tm-treehouse/lyrebird/model/notes-idle.md

# Idle-channel behaviour, and what the element lines do to the reference

Run: `./.venv/bin/python model/run_idle.py`. Logs in `results/idle.txt` and
`results/reference-current.txt`, figures `figures/idle_window.png` and
`figures/idle_blast.png`.

Two findings, in the order they were made. The first closes an open item: the
low-frequency limit cycle was a measurement artifact. The second opens a
larger one: **the element transition rate is a rectified copy of the signal,
it puts a signal-correlated current on the rail that sets full scale, and the
rotation creates that correlation rather than whitening it.** Section H.

## The headline (first finding: the limit cycle)

`notes-programme.md` reached the same conclusion independently and from a
different reproduction, at 96 kHz with one percent elements rather than the
176.4 kHz reference row. Two unrelated routes to the same 12-bin main lobe.

**The 15 to 19 dB loss is a measurement artifact, not a loop fault.** The
tripped run README.md reports at 125.06 dB measures **143.40 dB** when the
*windowed* mean is removed from the same record instead of the arithmetic
mean, and **143.69 dB** when the same trajectory is measured over 2^21 with
nothing else changed. Both agree with the 143.31 dB its neighbour in the table
reports.

The same term is behind two other published results:

* **The 15.7 dB attributed to round-half-up is the same artifact.** Corrected,
  half-up and ties-to-even differ by 0.01 dB. Section D.
* **The capacitor-tolerance table in `results/analog.txt` (Q2e) is 12.5 to
  15.7 dB low on every row, and its cost column is wrong by up to 3.2 dB.**
  Section F5.

Everything else checked is unaffected, to 0.01 dB. The full list is in
section F.

There is a real effect underneath all of it, and it is 128 dB down and below
the audio band.

## A. What a 2^20 transform does to a 20 Hz question

The tripped 176.4 kHz run reproduces exactly, so it can be taken apart.

| | |
| --- | --- |
| Kaiser beta 26 main lobe half-width | 12 bins |
| 2^20 bin width at 22.5792 MHz | 21.53 Hz |
| so the DC main lobe reaches | +/-258 Hz |
| shortest transform keeping it below 20 Hz | 13.55 M samples, 2^23.7 |

At 2^20 the DC main lobe covers the whole 20-100 Hz band and most of
100 Hz-2 kHz. **At that record length, near-DC energy and low-band energy are
not different measurements.**

And the loop always has near-DC energy, for a reason that has nothing to do
with limit cycles. The output takes eight levels spaced 2/7 apart, so the mean
of an N-sample record can only sit on a grid of (2/7)/N:

| Window | One unbalanced sample is |
| --- | --- |
| 2^20 | -128.3 dBFS |
| 2^22 | -140.3 dBFS |
| 2^23 | -146.3 dBFS |
| 2^24 | -152.4 dBFS |

Measured on the tripped record, per 2^20 block, as a count of unbalanced
samples: `+1.00 -1.00 +1.00 -1.00 +0.00 +0.00 -0.00 +0.00`. One sample per
million, alternating sign. That is a -128.3 dBFS component at about 10.8 Hz —
the smallest non-zero value the output alphabet can express over that window.

### The same 2^20 record, measured two ways

| Mean removed | SNDR | 20-100 Hz | 0.1-2 kHz | 2-20 kHz |
| --- | --- | --- | --- | --- |
| arithmetic (`x - x.mean()`) | 125.06 dB | -130.2 dBFS | -3.7 | -148.4 |
| windowed | **143.40 dB** | **-172.9 dBFS** | -3.7 | -148.4 |

**18.34 dB of the reported figure is the arithmetic mean not being the mean
the transform sees.** The Kaiser weights the centre of the record far above
its ends, so a record whose offset drifts across the window still has a DC bin
after `x - x.mean()`, and that bin's main lobe lands in the lowest audio bins.
Subtracting the windowed mean, `x - sum(w*x)/sum(w)`, removes it exactly. It
is one line and costs nothing:

```python
w = spectra.analysis_window(len(x))
x = x - (w * x).sum() / w.sum()
```

### The same trajectory over longer windows, nothing corrected

Plain mean removal throughout, i.e. the original method:

| Window | Bin | DC lobe reaches | SNDR | 20-100 Hz | below 20 Hz |
| --- | --- | --- | --- | --- | --- |
| 2^20 | 21.53 Hz | 258 Hz | 125.06 dB | -130.2 dBFS | (no bins) |
| 2^21 | 10.77 Hz | 129 Hz | 143.69 dB | -173.9 dBFS | -187.5 dBFS |
| 2^22 | 5.38 Hz | 65 Hz | 143.94 dB | -174.2 dBFS | -189.7 dBFS |
| 2^23 | 2.69 Hz | 32 Hz | 144.11 dB | -173.4 dBFS | -182.0 dBFS |

**The loss is gone by 2^21 and does not come back.** It was never in the loop.

## B. The trip rate on near-idle material

180 trials: `material.py`'s idle catalogue, six rates, six preambles each, so
the state the loop is in when the signal goes quiet differs from trial to
trial. Window 2^23 (341 ms, 2.93 Hz bins), preamble 2^19 element samples
discarded — longer than the cascade's settling, because a window that starts
inside the cascade's ring on the transition to silence reads -50 dBFS of
low-frequency energy and looks exactly like the fault being hunted.

20 Hz to 100 Hz of the element sum, over all 180 trials:

| Idle material | Corrected | Measured as before |
| --- | --- | --- |
| digital silence | -324 to -346 dBFS | -130 to -341 dBFS |
| small DC offset, -60 dBFS | -321 to -331 dBFS | -129 to -145 dBFS |
| after a fade to silence | -147 to -153 dBFS | -37 to -45 dBFS |
| digital silence, dithered source | -162 to -175 dBFS | -130 to -176 dBFS |
| near silence, -100 dBFS | -126 to -140 dBFS | -126 to -148 dBFS |

Counting a trial as tripped when its 20-100 Hz figure is more than 10 dB above
its own cell's median: **22 of 180 (12%) as before, against the 1-in-36 (3%)
reported for tones. Corrected, 6 of 180** — and those six are spreads between
-324 and -344 dBFS inside the digital-silence cells, which is numerical dust
190 dB below anything audible. At any threshold set in physical units rather
than relative to a median, the corrected rate is **0 of 180**.

The fade rows are the interesting ones for the old method: -37 to -45 dBFS
where the truth is -147 to -153 dBFS, a 110 dB error, because a fade leaves
exactly the slow drift across the window that plain mean removal cannot
remove.

## C. Conditions

No condition brings it on, because there is nothing to bring on.

* **DC at the modulator input**, swept 0 and -160 to -60 dBFS including a
  linear sweep through the -133 to -119 dBFS range where a first-order loop's
  correction rate would land in 20-100 Hz: in-band stays -173 to -181 dBFS and
  all of it is the shaped floor above 2 kHz; the 20-100 Hz band runs -318 to
  -344 dBFS. **A third-order loop with an eight-level quantizer does not lock
  to a constant.**
* **Input level**, near silence swept -60 to -140 dBFS: the output tracks the
  input's own noise and nothing else appears.
* **Where a fade ends**, fades from -3 to -80 dBFS: no effect.
* **The state and the pointer entering the window**: integrator states span
  roughly ±0.2 and the rotation pointer takes all seven values; correlation of
  either with the 20-100 Hz result is within ±0.2, i.e. nothing.
* **The rotation pointer is genuinely periodic at idle** — codes alternate 3
  and 4, so the pointer advances by 7 every two samples and returns to where it
  started, and every code lights the same elements every time. With 1% elements
  that shows up as a static output offset, not as noise: the in-band figure
  does not move.

## D. The 15.7 dB attributed to round-half-up is the same artifact

`run_endtoend.rounding_rule` rerun today reproduces the shape of the published
table but at a *different rate*: 44.1 kHz reads 124.73 against ties-to-even's
137.55, where README.md reports the loss at 96 kHz. That alone is the
giveaway — half-up leaves the same offset at every rate, so a fault caused by
the offset cannot move between rates from one run to the next. A lottery over
records can.

Same records, four measurements:

| Rate | Rounding | DC at mod in | 2^20 plain | 2^20 windowed | 2^22 windowed |
| --- | --- | --- | --- | --- | --- |
| 48 kHz | half up | -168.7 dBFS | 137.56 | 137.57 | 138.41 |
| 48 kHz | half even | -203.0 | 137.54 | 137.54 | 138.42 |
| 96 kHz | half up | -169.6 | 140.23 | 140.23 | 141.39 |
| 96 kHz | half even | -193.8 | 140.23 | 140.25 | 141.41 |
| 192 kHz | half up | -169.2 | 143.76 | 143.82 | 144.35 |
| 192 kHz | half even | -204.1 | 143.83 | 143.83 | 144.35 |
| **44.1 kHz** | **half up** | **-169.0** | **124.73** | **137.53** | **137.98** |
| 44.1 kHz | half even | -210.3 | 137.55 | 137.55 | 137.99 |
| 88.2 kHz | half up | -170.3 | 140.14 | 140.15 | 140.88 |
| 88.2 kHz | half even | -187.3 | 140.15 | 140.15 | 140.88 |
| 176.4 kHz | half up | -169.8 | 143.20 | 143.33 | 144.10 |
| 176.4 kHz | half even | -196.8 | 143.31 | 143.33 | 144.07 |

**Measured as published, half-up is up to 12.8 dB worse. Measured properly it
is 0.01 dB worse.**

What survives: half-up does leave a real static offset at the modulator input,
-168.7 to -170.3 dBFS against -187.3 to -210.3 dBFS for ties to even, and that offset
does reach the output as DC. Convergent rounding removes it and costs one
adder's difference, so **the recommendation stands**. The reason given for it
does not.

The sentence in README.md that needs to go is "a delta-sigma loop turns a
static input offset into idle tones at the bottom of the audio band", together
with the table that appears to demonstrate it. At -169 dBFS it does not,
measurably.

## E. The 1-in-36 count, recounted

`run_endtoend.limit_cycles` rerun unchanged — six rates, six input
perturbations, with and without 0.25 LSB of dither at the quantizer — with the
same records measured both ways:

| Measurement | Runs more than 5 dB below their row median |
| --- | --- |
| as published: 2^20, arithmetic mean | **1 of 72** |
| same records: 2^20, windowed mean | **0 of 72** |
| same records: 2^22, windowed mean | **0 of 72** |

The published rate reproduces exactly and disappears exactly. The one that
trips as published is 176.4 kHz with 0.25 LSB of dither, reading 124.9 dB
against its row's 143.3 dB; corrected it reads 143.3 dB like the rest.

**Dither was never moving the fault around.** Every remedy changes the record,
every record leaves a different residue on the (2/7)/N grid, and the short
window reports the residue. Nothing was being done to the loop in either
direction. A second remedy that "only moves it" would have meant the same
thing, which is the argument for fixing the measurement rather than trying a
third.

## F. Blast radius

`x - x.mean()` is used at five sites that produced published figures. Each row
below is **one record measured twice**, not two runs, so the difference is the
mean removal and nothing else.

### F1. End to end per rate, and the chain as it will be built

| Rate | Elements | As published | Corrected (2^20) | Moved by |
| --- | --- | --- | --- | --- |
| 48 kHz | matched | 137.57 | 137.57 | -0.00 |
| 48 kHz | 1% | 132.92 | 132.92 | -0.00 |
| 96 kHz | matched | 140.27 | 140.29 | +0.01 |
| 96 kHz | 1% | 133.72 | 133.73 | +0.00 |
| 192 kHz | matched | 143.83 | 143.83 | +0.00 |
| 192 kHz | 1% | 133.97 | 133.97 | +0.00 |
| 44.1 kHz | matched | 137.56 | 137.56 | +0.00 |
| 44.1 kHz | 1% | 132.84 | 132.84 | +0.00 |
| 88.2 kHz | matched | 140.18 | 140.18 | +0.01 |
| 88.2 kHz | 1% | 132.83 | 132.83 | +0.00 |
| **176.4 kHz** | **matched** | **125.06** | **143.40** | **+18.34** |
| 176.4 kHz | 1% | 133.32 | 133.32 | +0.00 |

**One row of twelve moves.** It is the one README.md already flags with an
asterisk in the datapath verification table. Everything else is correct as
printed, including the 132.8 dB worst case the hardware is held to.

### F2, F3, F4. Rotation, volume placement, order sweep

Nothing moves, to 0.01 dB, in any row:

* element mismatch and rotation (`run_experiments.py:210`), 10 rows at 2^21,
  orders 2 and 3, mismatch 0/0.1/1%, rotation on and off — max move 0.00 dB;
* volume at the chain input against volume at the modulator input, 8 rows —
  max move 0.01 dB;
* the modulator order sweep, orders 2 to 5 — max move 0.00 dB.

So the rotation recommendation, the 33.3 dB mismatch correction, the "volume
goes at the modulator input" result and the order choice are all unaffected.

### F5. The analog section: `results/analog.txt` Q2e was wrong on every row

**Re-run and fixed.** `run_analog.py` was rerun after the correction went in,
and the diff against the old log is **ten lines: the Q2e table and nothing
else** in the whole analog study. The corrected matched row is 132.93 dB
against the reference row's 132.92 dB quoted in the sentence below it, which is
the check that says the new numbers are the right ones — a pole three decades
above the band should cost nothing, and now it measures as costing nothing.

The table as it stood:

This is the second real casualty. The capacitor-tolerance table applies a
1 MHz pole per element to the 48 kHz, 1% element record and re-measures.

| C tolerance | As published | Corrected (2^20) | Corrected (2^21) | Moved by |
| --- | --- | --- | --- | --- |
| matched | 120.43 | 132.93 | 133.75 | +12.50 |
| 2% | 119.98 | 132.94 | 133.75 | +12.96 |
| 5% | 119.34 | 132.93 | 133.73 | +13.59 |
| 10% | 118.37 | 132.84 | 133.62 | +14.47 |
| 20% | 116.70 | 132.41 | 133.15 | +15.70 |

And the column the table exists for, the cost of tolerance:

| C tolerance | Cost as published | Cost corrected |
| --- | --- | --- |
| 2% | +0.45 dB | -0.01 dB |
| 5% | +1.09 dB | -0.01 dB |
| 10% | +2.06 dB | +0.08 dB |
| 20% | +3.72 dB | +0.52 dB |

The corrected matched row, 132.93 dB, is the reference row's own 132.92 dB to
0.01 dB — which is the check that says the corrected numbers are the right
ones, because a pole three decades above the band should cost nothing and now
does. `results/analog.txt` currently prints a matched row 12.5 dB below the
reference it quotes in the following sentence, and does not reconcile the two.

The conclusion drawn there is unchanged and in fact stronger: ordinary C0G
parts are adequate, 20% tolerance costs 0.52 dB rather than 3.72 dB.

## Which published numbers in README.md are wrong

1. **The "which way ties go" table**, and the claim that half-up costs 15.7 dB
   worst case. Corrected, the worst case is 0.01 dB. The recommendation
   survives; the justification does not.
2. **The low-frequency limit cycle section in full.** There is no limit cycle.
   The 125.1 dB figure, the 15-19 dB range, the 1-in-36 rate and the statement
   that dither moves which run trips are all descriptions of the transform.
3. **The asterisked 176.4 kHz reference row** in the datapath verification
   table, 125.06 dB, is 143.40 dB.

Everything else checked — every per-rate figure, the 132.8 dB worst case, the
rotation table, the order sweep, the volume placement, the datapath widths —
is correct as printed.

Outside README.md, `results/analog.txt`'s Q2e table needs re-running.

## What the real effect is, and why it does not matter

The loop's output over any finite window carries a residual DC of a few times
(2/7)/N, because the output alphabet cannot express the input's mean exactly
over a finite record. Over 2^20 samples that is one sample in a million, a
-128.3 dBFS component at around 10 Hz. It is:

* below the audio band, not in it;
* at the smallest level the output alphabet can express over that window, so
  it cannot be reduced by anything in the digital design;
* removed from the output by the coupling capacitor the design already has.

It is not a limit cycle, it is not periodic, and nothing in the loop is
locking. The rest of this note's measurements confirm that directly.

## H. The reference rail: the transition rate is not whitened, it is rectified

Run by `run_idle.py H`, log in `results/reference-current.txt`. This answers a
question the hardware thread raised in
`hardware/lyrebird-dac-reva/parts-notes.md`: the 180 pF filter capacitors and
the registers draw current in proportion to how often element lines *change*,
0008's constant-current guarantee covers only the DC term, and the reference
rail is a multiplier on the output, so a signal-correlated current there is
distortion.

**Read this as a prediction, not a measurement.** The model has no supply in
it. What is measured is a digital proxy — how many element lines change state
each clock — converted through hardware constants transcribed from
`hardware/lyrebird-dac-reva/`. Every step is stated in the log so it can be
rechecked or rescaled. A bench measurement of the rail with the modulator
running is what would settle it.

### The answer: correlated, and the rotation creates the correlation

Not whitened. The transition rate is a **full-wave rectified copy of the
signal**, and two exact identities say why. With `k` and `k'` consecutive
codes, measured over 2^21 samples and confirmed bit-exact:

| Selection rule | Lines that change per sample |
| --- | --- |
| plain DWA | `T = 2·min(k+k', 14−k−k')` |
| no rotation | `T = 2·|k−k'|` |

With rotation the pointer advances **by the code**, so consecutive windows are
disjoint until they wrap and the count is `k+k'` folded about seven. Writing
`k = 3.5 + s`:

```
T  =  14 − 4|s|
```

A rectifier. Its spectrum is the even harmonics of the signal. Checked two
ways before being believed:

| | Closed form | Simulated |
| --- | --- | --- |
| mean, 1 kHz at -3.7 dBFS | 8.179 | 8.155 |
| second harmonic amplitude | 3.881 transitions | 3.834 transitions |

and the null tests hold: digital silence and a DC input both put the 2 kHz
component at ~1e-3 transitions against 3.83 with the tone, and the second
harmonic scales with amplitude as the closed form says down to about
-16 dBFS, below which the loop's own noise fills in the rectification.

### No selection rule separates the two properties

`SNDR 1%` is the ordinary in-band figure with one percent elements — what the
rotation exists to protect — beside the transition rate it costs:

| Rule | T mean | 2nd harmonic | SNDR, 1% elements |
| --- | --- | --- | --- |
| **plain DWA, advance by the code** | 8.155 | **3.834** | **133.79 dB** |
| no rotation | 1.188 | 0.019 | 57.05 dB |
| advance by 1 each sample | 4.020 | 0.052 | 84.23 dB |
| advance by 3 each sample | 7.987 | 3.512 | 84.82 dB |
| pointer stepped by an LFSR | 5.546 | 1.494 | 77.82 dB |
| both sides on one pointer | 7.505 | 3.632 | 81.33 dB |

**Everything that lowers the transition rate's signal content also destroys
the mismatch shaping, because they are the same mechanism.** DWA shapes
mismatch to first order precisely *because* the pointer advance equals the
code, and that is what ties the number of changing lines to the code. A fixed
step takes 37 dB off the transition rate and 50 dB off the mismatch figure.
This is not a pointer rule chosen badly; it is a property of the method. Four
alternatives were tried and all four failed — recorded so nobody tries them
again.

### Converted through the hardware constants

3.32 V rail, 1.668k+1.668k element, 180 pF per element (simulated with its RC,
τ = 150 ns against a 40.7 ns clock, so charge per transition is about a third
of C·V), 30 pF Cpd per flip-flop, 10 mΩ in-band rail impedance, 28 lines =
two channels of 14 given the same signal, which is the mono worst case.

| Term | Mean current | At 2f | Equivalent output error |
| --- | --- | --- | --- |
| capacitors only | 20.08 mA | 1.718 mA | -115.6 dBFS |
| registers only | 19.96 mA | 9.385 mA | -102.9 dBFS |
| **both** | **40.04 mA** | **11.103 mA** | **-101.1 dBFS** |

11.1 mA at 2 kHz on 10 mΩ is **111 µV on 3.32 V**, which is the hardware
thread's own -90 dB worst case arriving as the actual case rather than the
bound. The output error is odd-harmonic, as the mechanism demands — an even
modulation times an odd signal:

| Harmonic | 2 | 3 | 4 | 5 | 6 | 7 |
| --- | --- | --- | --- | --- | --- | --- |
| dBFS | -161.4 | **-101.1** | -159.7 | -121.2 | -160.7 | -131.5 |

**Against the -136.5 dBFS the chain is held to, this is 35 dB worse. Against
the 110 dB target, which is -113.7 dBFS at this level, it is 12.6 dB short.**
An end-to-end figure of about 97 dB where 132.8 dB is claimed.

Real material does not escape it: the transition rate follows the envelope, so
the ripple is the programme's own envelope and the products land under it.
Programme-like material gives -104.4 dBFS and sustained bass -99.0 dBFS.
Percussive material gives -138.3 dBFS, because its transition rate sits near
the top of its range most of the time and has little left to modulate.

### What would have to change

**Local decoupling is not the mitigation, and 0008 says it is.** The ripple is
at twice the signal frequency and at the programme envelope — an *audio*
frequency current. Eight 100 nF parts are 100 Ω at 2 kHz; the regulator's own
10 mΩ is what this current sees. The decoupling 0008 asks for is right for the
megahertz content and does nothing here. Reaching the chain's own floor would
take 35 dB less rail impedance in band, 170 µΩ at 2 kHz, which no regulator
does and which would need farads of bulk capacitance.

What the identity points at instead: `T = 14 − 4|s|` is bounded above by 14 and
the modulation is the deficit, so **a transition ballast** — dummy lines
toggled to make up the deficit, driven by the same code — would flatten the
current without touching the selection rule or the mismatch shaping. It costs
the average current of a fully toggling array, which is the opposite of a power
saving, and it is a hardware change rather than a model result. It is the one
mitigation the measurement actually points at.

### Cross-checks, because the result is large

An independent arithmetic route: a ripple of amplitude `G` at 2f against a
signal of amplitude `A` at f puts `A·G/2` on the third harmonic. Measured
against that, and swept over what the identity says should and should not
matter:

| Case | T mean | I at 2f | H3 | A·G/2 | diff |
| --- | --- | --- | --- | --- | --- |
| 48 kHz, 1 kHz, -3.7 dBFS | 8.155 | 11.103 mA | -101.14 | -99.23 | -1.91 |
| 192 kHz, 1 kHz, -3.7 | 8.155 | 11.103 mA | -101.14 | -99.23 | -1.91 |
| 44.1 kHz, 1 kHz, -3.7 | 8.155 | 10.364 mA | -101.71 | -99.83 | -1.88 |
| 48 kHz, 200 Hz, -3.7 | 8.155 | 11.103 mA | -101.14 | -99.23 | -1.91 |
| 48 kHz, 5 kHz, -3.7 | 8.155 | 11.103 mA | -101.14 | -99.23 | -1.91 |
| 48 kHz, 1 kHz, -10 | 11.133 | 4.773 mA | -116.35 | -112.87 | -3.48 |
| 48 kHz, 1 kHz, -20 | 12.936 | 0.974 mA | -137.85 | -136.68 | -1.18 |

Sample rate and tone frequency change nothing, which is what `T = 14 − 4|s|`
requires — the mean and second-harmonic amplitude of a rectified sine depend on
amplitude alone. The 44.1 kHz row differs because its element clock does, which
is the check that the pipeline is responding at all.

**Level changes it faster than the signal.** The ripple is proportional to
amplitude and the product to amplitude squared, so the third harmonic sits
97 dB below a -3.7 dBFS signal and 118 dB below a -20 dBFS one. This is a
large-signal mechanism, worst exactly where the 110 dB target is specified.

### How confident to be

The largest single uncertainty is the register's Cpd, which
`hardware/.../power.md` already flags: read as per package rather than per
flip-flop, the register row drops 24 dB and the capacitors-only row is the
answer. **Both rows are above the chain's own floor, so the uncertainty
changes the size of the problem, not whether there is one.** The other
assumptions worth challenging before acting: that the rail impedance really is
10 mΩ at 2 kHz, and that the element current is proportional to the rail to
first order with nothing else regulating it.

## What is now unmeasured, as opposed to corrected

Three published figures turned out to be the ruler rather than the chain. The
honest consequence is not only that those three numbers change. It is that
**the low-frequency behaviour of this loop has never been characterised. It has
only been mis-measured.** Every statement the repository held about it — the
wander, its 20-100 Hz confinement, its rate, its immunity to dither, its
sensitivity to 2^-40 — described the transform. Removing those statements
leaves a gap, not an answer, and the gap should be stated rather than left
implied by the absence of a section.

What this work does and does not establish below 100 Hz:

**Established.** Over 180 near-idle trials at 2^23 (341 ms, 2.93 Hz bins) the
20-100 Hz band of the element sum sits at -324 to -346 dBFS on digital silence
and -321 to -331 dBFS on a -60 dBFS DC input, and tracks the source's own noise
on everything else. A constant at the modulator input from -160 to -60 dBFS
produces no in-band tone. Over 72 tone runs at 2^20 and 2^22 nothing reads low.
That is a real negative result and it is enough to close the open item.

**Not established, and worth saying plainly:**

* **Nothing has been measured below 20 Hz on purpose.** The 20 Hz band edge was
  inherited from the audio-band convention and every measurement here treats
  sub-20 Hz energy as something to remove. The residue described above sits
  there. Its size is bounded by the (2/7)/N argument, which is arithmetic
  rather than measurement, and by the -167 to -190 dBFS the sub-20 Hz bins read
  at 2^23 — but that band has never been the subject of a measurement, only the
  thing being excluded from one.
* **Nothing longer than 341 ms has been run.** A wander slower than about 3 Hz
  is outside every record taken here, including the corrected ones. If the loop
  does something on a timescale of seconds, this work would not have seen it.
  `min_transform` says a transform whose DC lobe clears 20 Hz needs 2^24 at the
  element clock, which is 683 ms; the bulk trials ran at half that and lean on
  the windowed-mean removal to make up the difference.
* **The trip criterion was relative, not physical.** Trials were counted as
  tripped at 10 dB above their own cell's median, which is why 6 of 180
  "tripped" corrected at levels between -324 and -344 dBFS. No threshold in
  physical units has been set for what would constitute an idle-channel fault
  worth acting on, because nothing came close enough to need one.
* **No hardware has confirmed any of it.** All of the above is a float64 model
  of an exact loop. The idle-channel behaviour that matters is the analog
  section's, and the residue discussed here is 128 dB below full scale at a
  frequency the output coupling removes.

The correct summary is therefore: **there is no evidence of a low-frequency
limit cycle, and the evidence that was thought to exist was an artifact.** That
is weaker than "the loop is clean below 100 Hz", and it is what the
measurements support.

## What was changed in the tree

**The measurement is fixed at source, not per site.** `spectra.remove_dc`
subtracts `sum(w*x)/sum(w)` and carries the explanation; `spectra.Measurement`
calls it for every measurement, so a sixth measurement site cannot reintroduce
this by forgetting. `Measurement.of(..., dedc=False)` reproduces the old
behaviour and exists only so `run_idle.py` can show both on one record.

The five sites that had `x - x.mean()` now call `spectra.remove_dc`:

| Site | What it fed |
| --- | --- |
| `lyrebird_model/endtoend.py:232` | every end-to-end table |
| `run_experiments.py:210` | rotation and mismatch |
| `run_analog.py:113` | the analog records |
| `run_analog.py:623` | the capacitor-tolerance table |
| `run_endtoend.py:443` | the limit-cycle count |

Regenerated: `results/idle.txt`, `results/analog.txt` (Q2e only; ten lines
changed in the whole log), `figures/idle_window.png`, `figures/idle_blast.png`.

Corrected: `README.md` — the ties section, the asterisked 176.4 kHz row, the
limit-cycle section replaced outright, a new entry in the measurement traps,
and a note at the top saying the earlier figures were wrong.
`docs/open-items.md` — the limit cycle closed.

**Not changed, and worth a look from whoever owns it:**
`lyrebird_model/material.py` still describes the limit cycle as real in three
docstrings (module header, `dc_offset`, `band_shape`). The module itself is
exactly right and was the correct instrument for this; only its prose is now
stale. It was left alone because `run_programme.py` is working in the same
file.
