tm-treehouse/lyrebird/docs/review/2026-09-21/docs-audit.md

# Documentation and decision-record audit

**Scope.** `docs/decisions/0001`–`0013` and their index, `docs/open-items.md`,
`README.md`, `hardware/README.md`, `hardware/interface.md`, `model/README.md`,
`hardware/lyrebird-*-reva/brief.md` and `power.md`, and
`hardware/lyrebird-dac-reva/parts-notes.md`.

This review checks the project's account of itself against the netlists, the
model logs and the HDL. It does not review the design. Nothing was changed.

Two findings already published elsewhere are not re-derived here and are not
counted again: `open-items.md:177`'s retracted 0.5 dB figure and
`hardware/README.md:190-198`'s invented mismatch table (dsp-model.md H3), and
interface.md's oscillator naming and the false "604 Ω because of the 50 mA LDO"
reason (output-module.md). They are referenced where a verdict depends on them.

---

## 1. Verdicts on the thirteen decision records

Each record is judged against the current netlists, `model/results/`, the HDL
and `docs/open-items.md`. "Marked" means the record's own **Status:** line or
an in-file correction tells a reader what changed; the index at
`docs/decisions/README.md` is judged separately because it is what a reader
scans first.
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
