tm-treehouse/lyrebird/model/figures/idle_blast.png

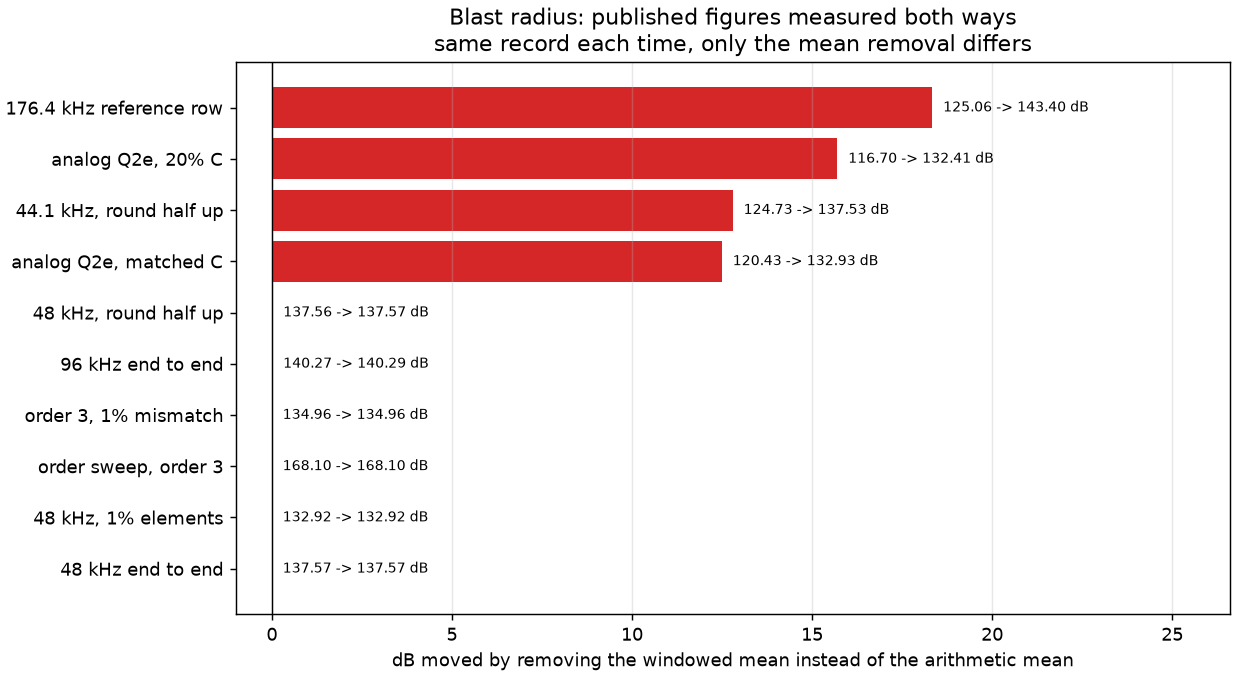
model/figures/idle_blast.png
