tm-treehouse/lyrebird/model/figures/idle_window.png

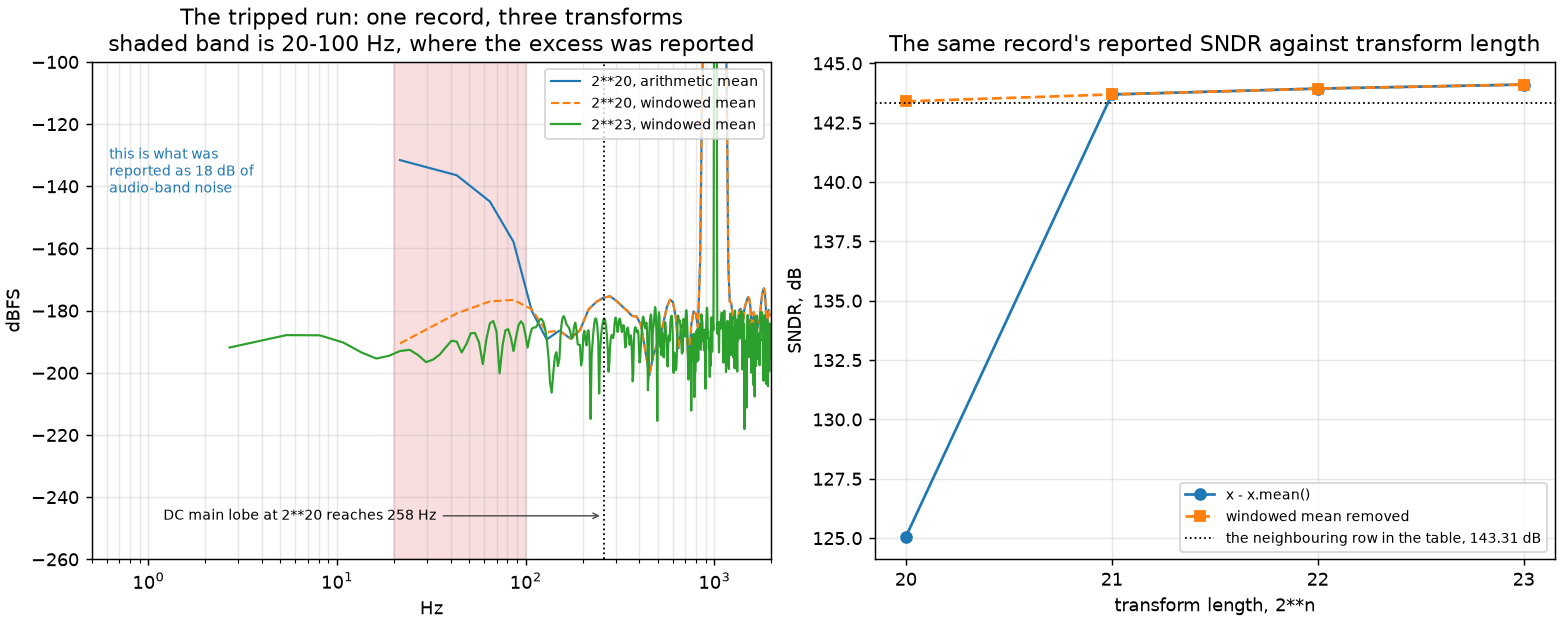
model/figures/idle_window.png
