tm-treehouse/lyrebird/model/figures/mismatch_rotation.png

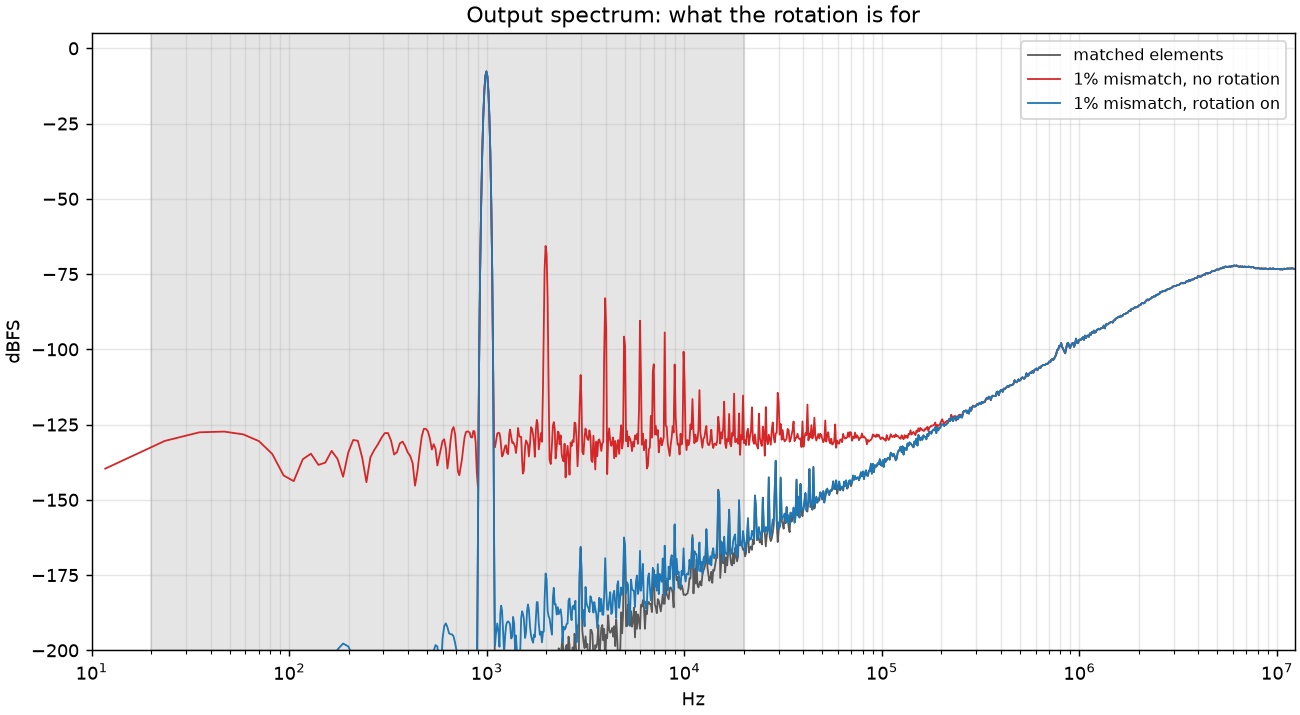
model/figures/mismatch_rotation.png
