tm-treehouse/lyrebird/model/figures/programme_headroom.png

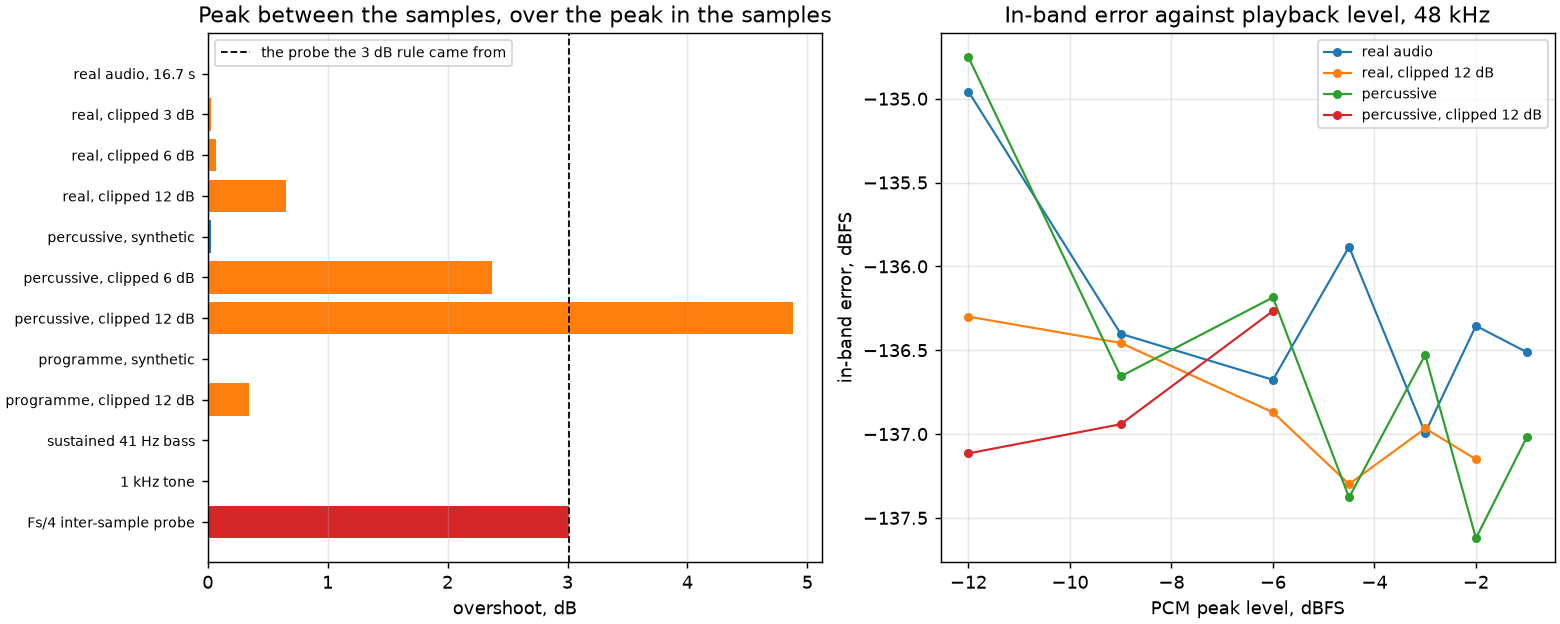
model/figures/programme_headroom.png
