tm-treehouse/lyrebird/model/figures/programme_mismatch.png

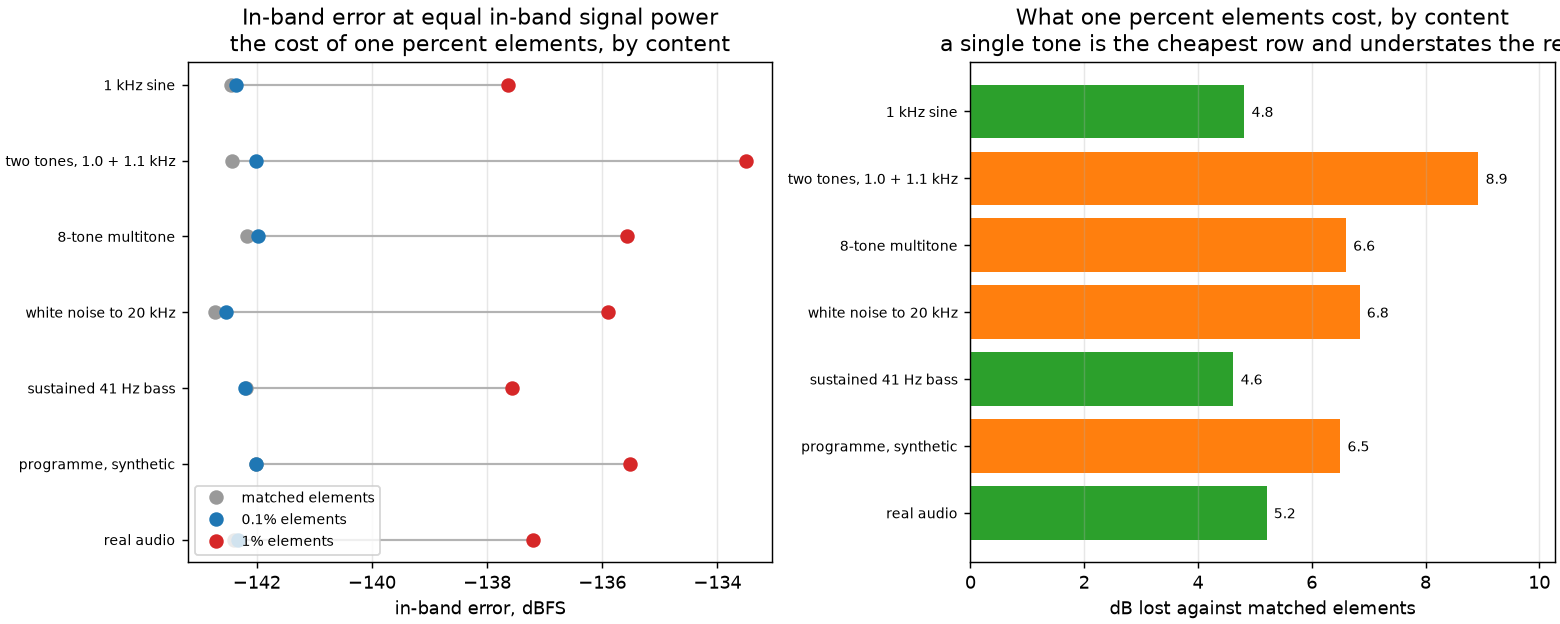
model/figures/programme_mismatch.png
