tm-treehouse/lyrebird/model/figures/programme_shape.png

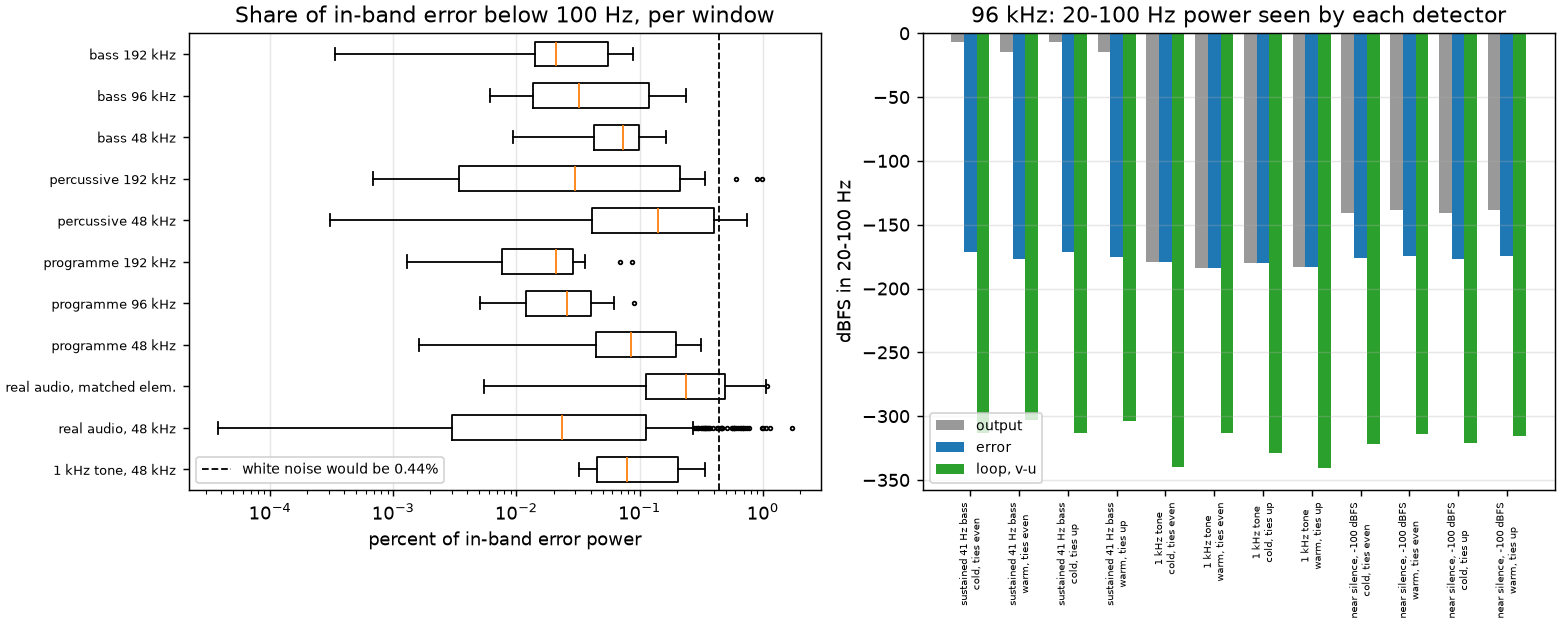
model/figures/programme_shape.png
