tm-treehouse/lyrebird/model/figures/programme_windows.png

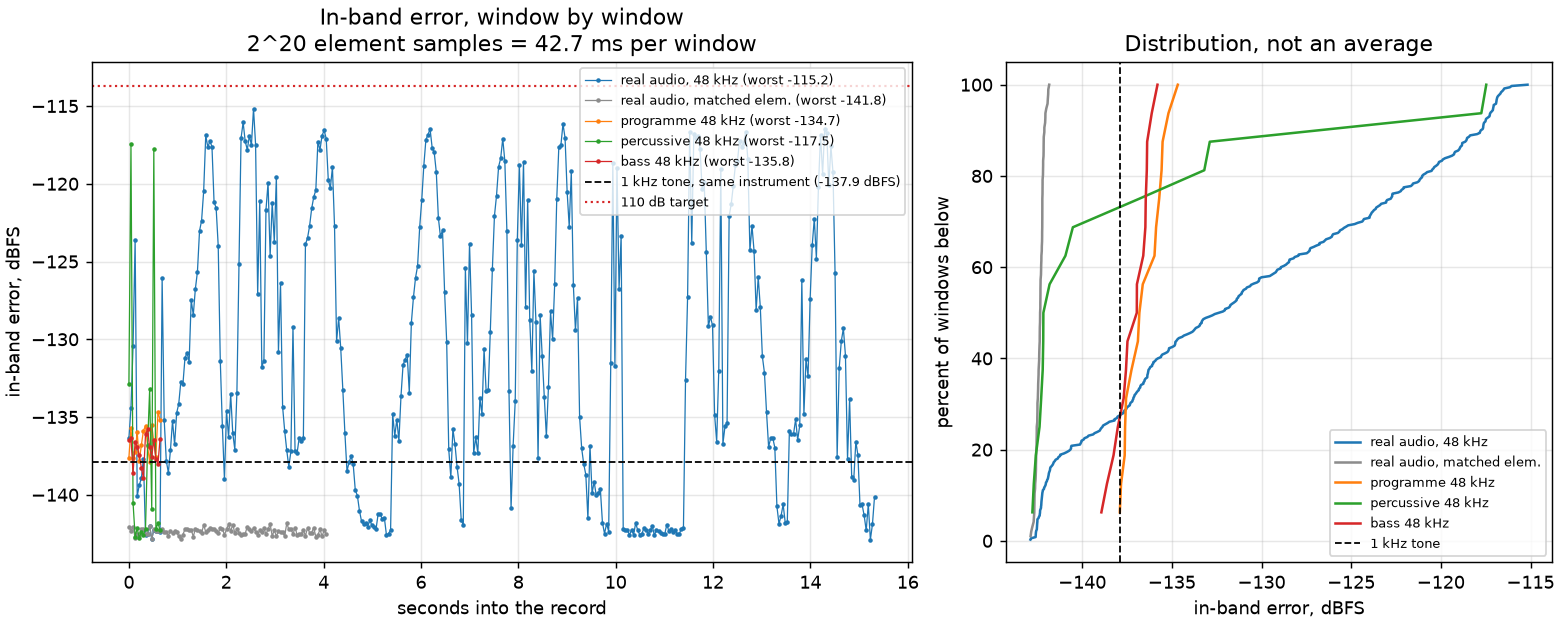
model/figures/programme_windows.png
