tm-treehouse/lyrebird/model/figures/order_sweep.png

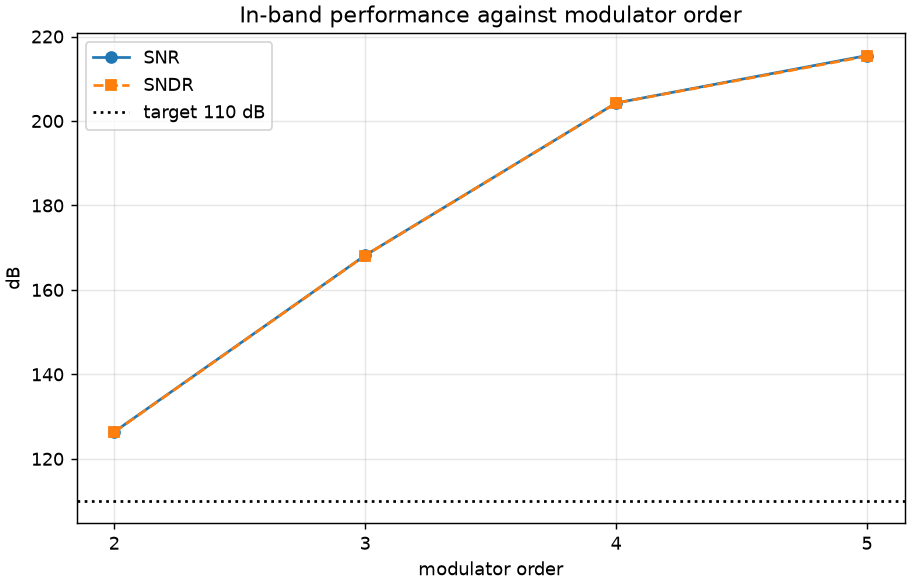
model/figures/order_sweep.png
